superlou/deskbot/cad/HXT900/hxt900.png

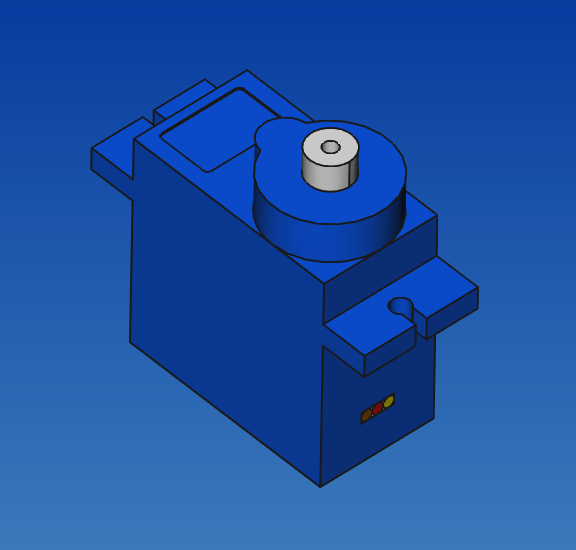
cad/HXT900/hxt900.png
