superlou/deskbot/blender/mockup.blend.png

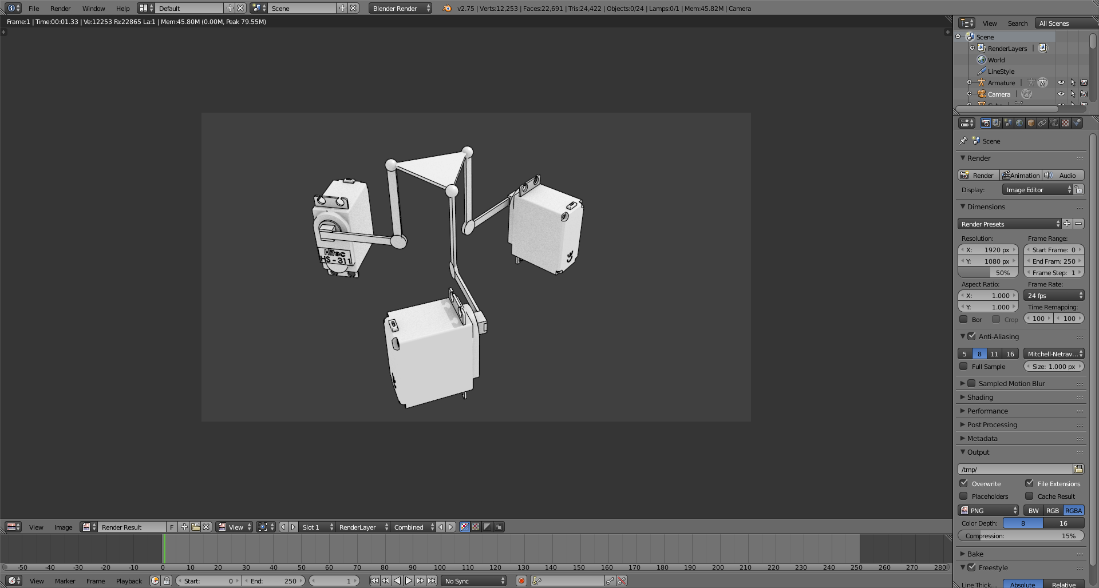
blender/mockup.blend.png
