superlou/deskbot/blender/sketch_render.png

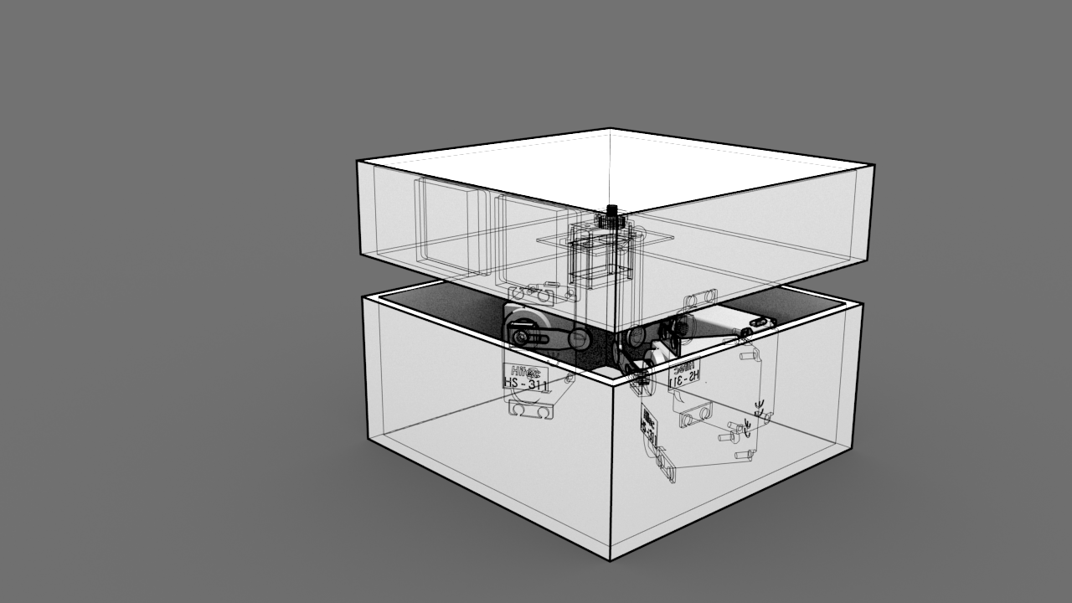
blender/sketch_render.png
