superlou/deskbot/blender/sketch_render_no_box.png

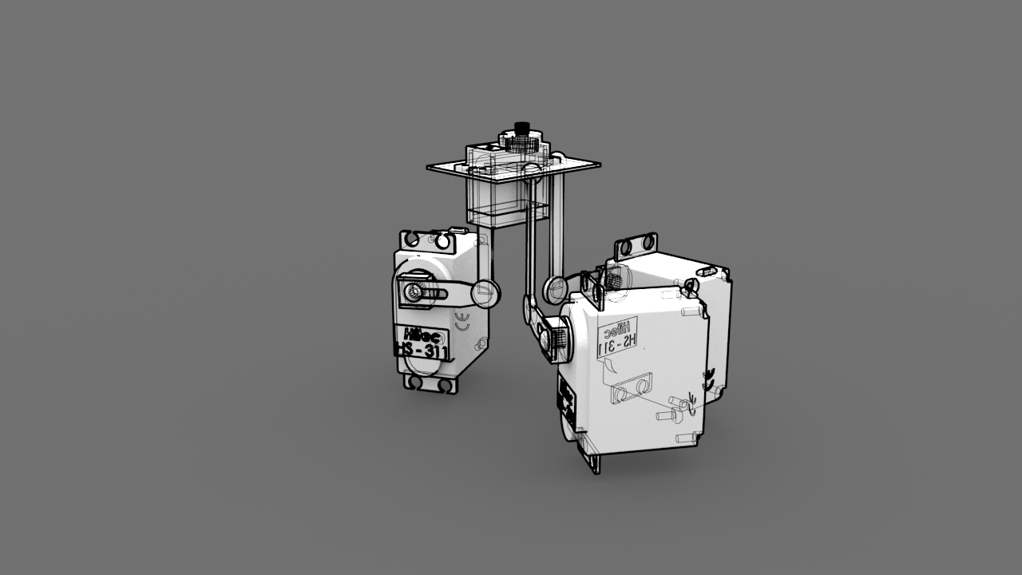
blender/sketch_render_no_box.png
