superlou/deskbot/diagrams/constrains.png

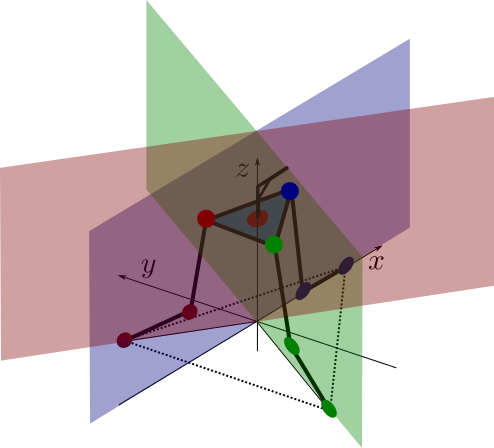
diagrams/constrains.png
