superlou/deskbot/diagrams/leg_model.png

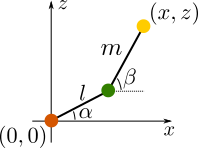
diagrams/leg_model.png
