superlou/deskbot/diagrams/leg_solutions.png

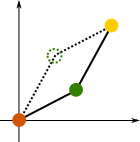
diagrams/leg_solutions.png
