superlou/deskbot/diagrams/simple_platform.png

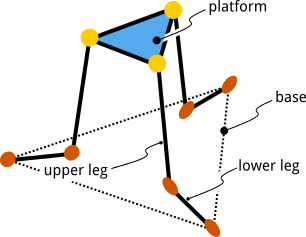
diagrams/simple_platform.png
