superlou/deskbot/cad/servo/Hitec HS-311 Servo Motor/Spline.SLDPRT

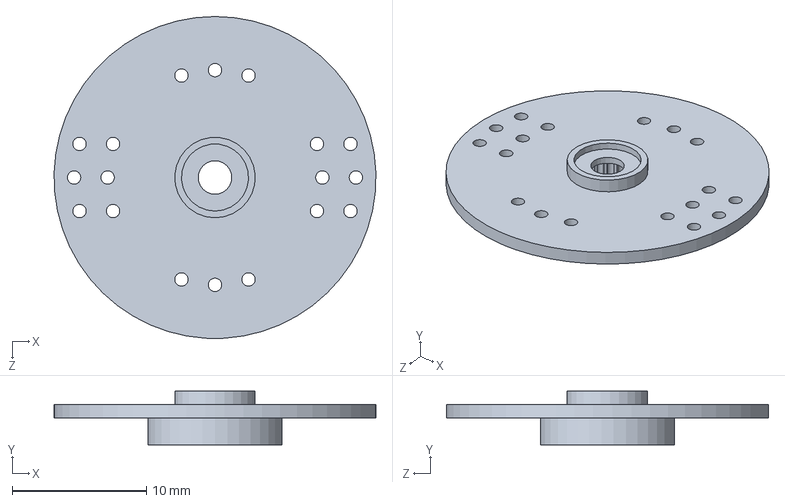
[picture p27: CAD file, 2015-07-31]
cad/servo/Hitec HS-311 Servo Motor/Spline.SLDPRT
24.0 x 4.00 x 24.0 mm
