superlou/deskbot/cad/servo_horn.fcstd

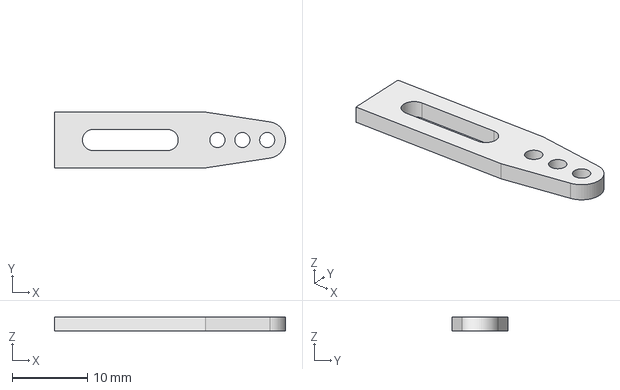
[picture p28: CAD file, 2016-11-07]
cad/servo_horn.fcstd
30.6 x 7.40 x 1.90 mm
