superlou/deskbot/cad/clevis.fcstd

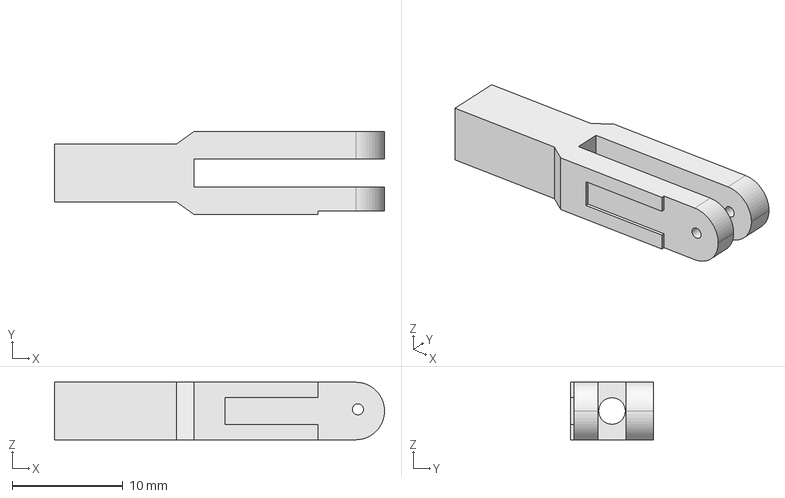
[picture p29: CAD file, 2016-11-07]
cad/clevis.fcstd
29.8 x 7.50 x 5.20 mm
