superlou/deskbot/cad/hs-311_pinion_adapter.fcstd

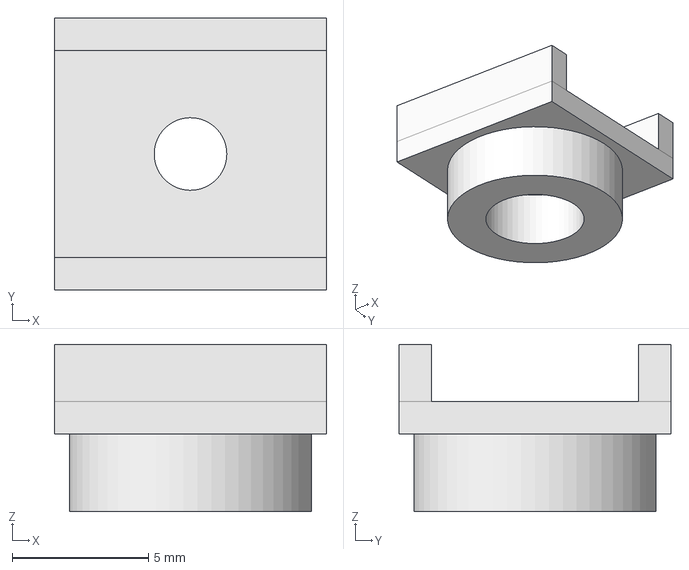
[picture p30: CAD file, 2016-11-07]
cad/hs-311_pinion_adapter.fcstd
10.0 x 10.0 x 6.15 mm
