superlou/deskbot/cad/threaded_ball.fcstd

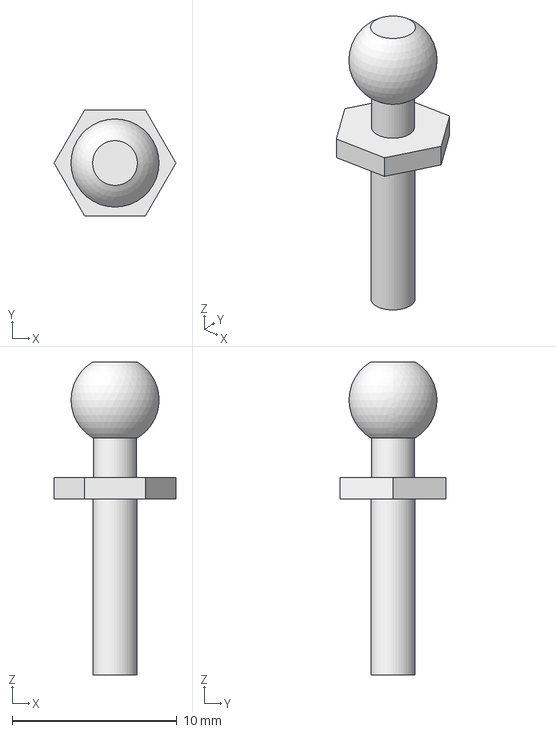
[picture p31: CAD file, 2016-11-07]
cad/threaded_ball.fcstd
7.39 x 6.40 x 19.0 mm
