superlou/deskbot/cad/base.fcstd

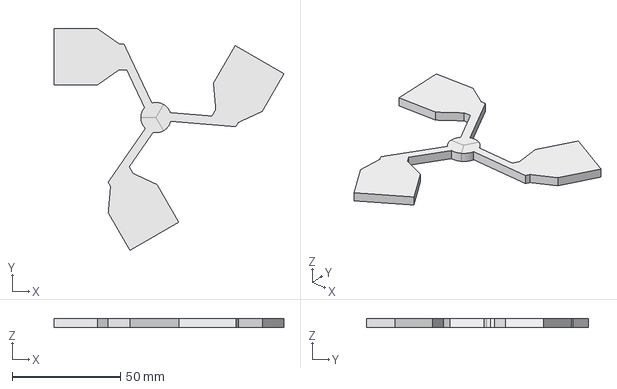
[picture p32: CAD file, 2016-07-19]
cad/base.fcstd
106.0 x 102.2 x 4.00 mm
