superlou/deskbot/cad/crown2.fcstd

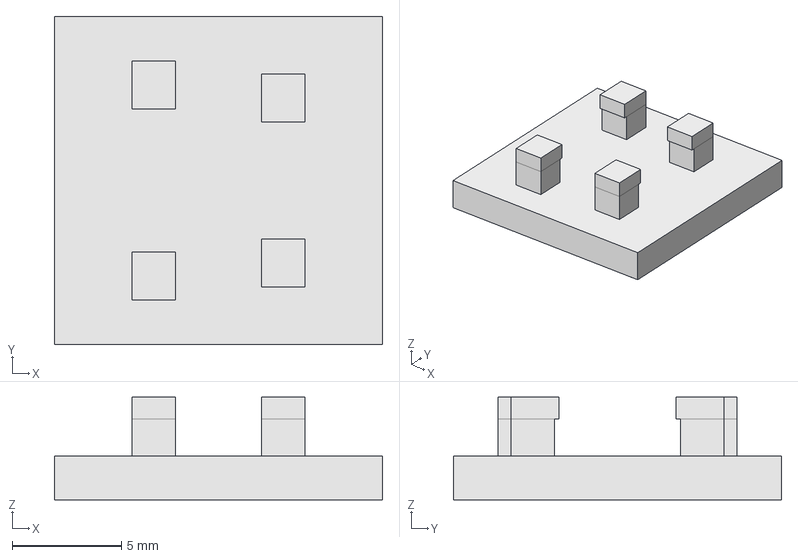
[picture p33: CAD file, 2016-07-19]
cad/crown2.fcstd
15.0 x 15.0 x 4.70 mm
