superlou/deskbot/cad/flat_servo_stand.fcstd

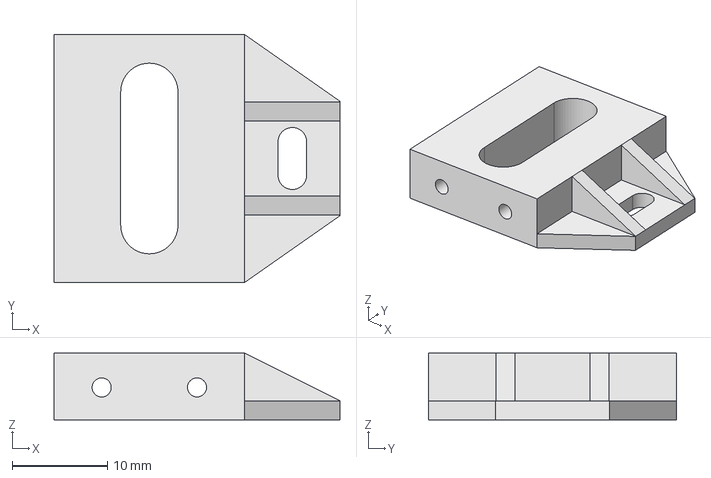
[picture p34: CAD file, 2016-07-19]
cad/flat_servo_stand.fcstd
30.0 x 26.0 x 7.00 mm
