superlou/deskbot/cad/crown.fcstd

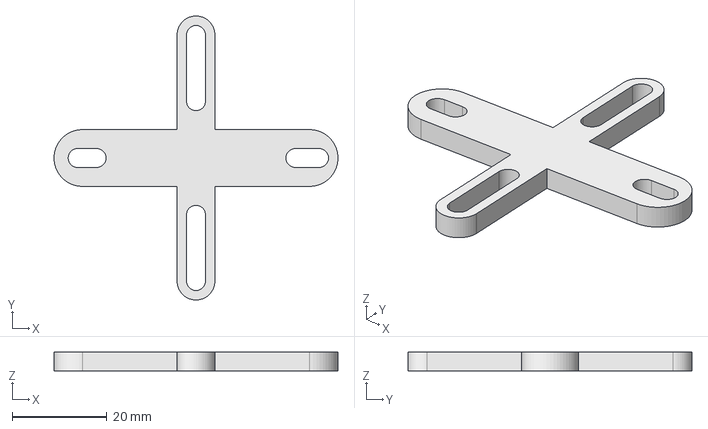
[picture p35: CAD file, 2016-07-19]
cad/crown.fcstd
60.0 x 60.0 x 4.00 mm
