superlou/deskbot/cad/plate.stl

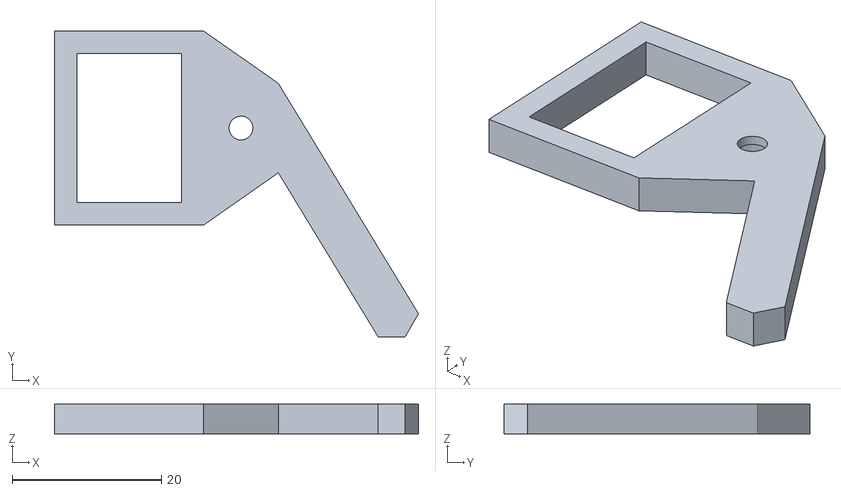
[picture p36: CAD file, 2016-07-19]
cad/plate.stl
48.8 x 41.0 x 4.00
