superlou/deskbot/cad/servo_and_flat_stand.fcstd

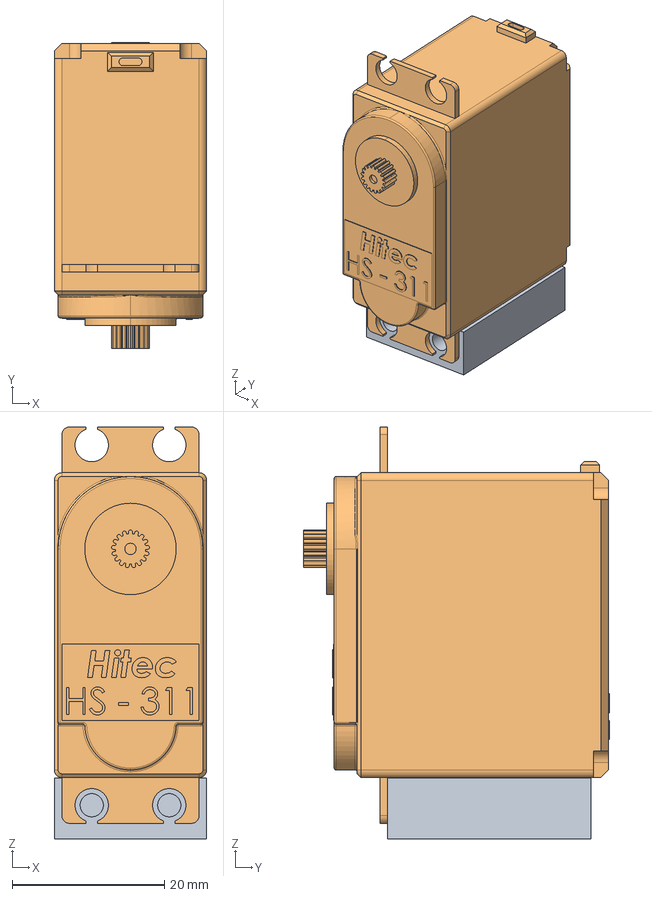
[picture p37: CAD file, 2016-04-03]
cad/servo_and_flat_stand.fcstd
20.0 x 40.1 x 54.1 mm
flat_servo_stand_01
servo_hs_311_01
