superlou/deskbot/cad/thin_servo_stand.fcstd

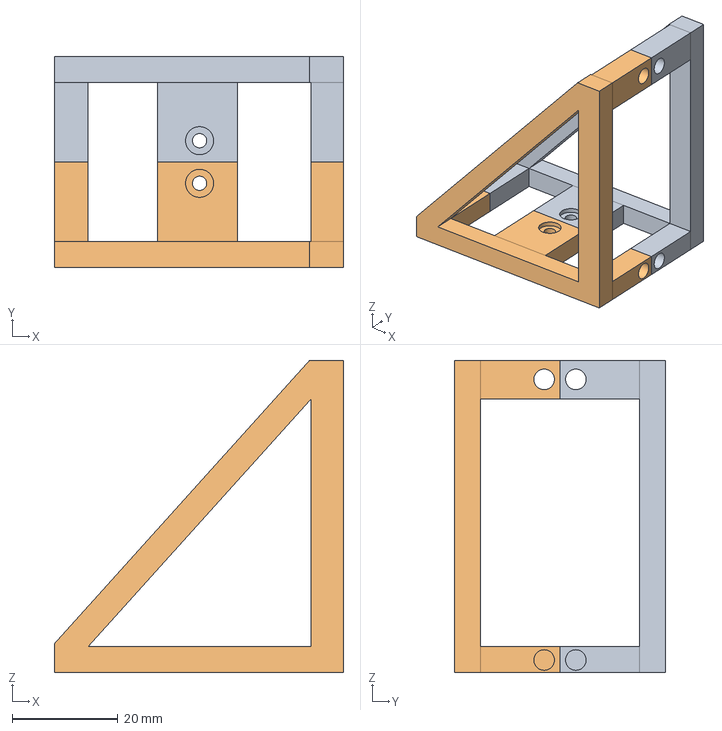
[picture p38: CAD file, 2015-12-17]
cad/thin_servo_stand.fcstd
54.8 x 40.0 x 59.0 mm
Pocket002 (Mirror #1)
