superlou/deskbot/cad/test_mount.step

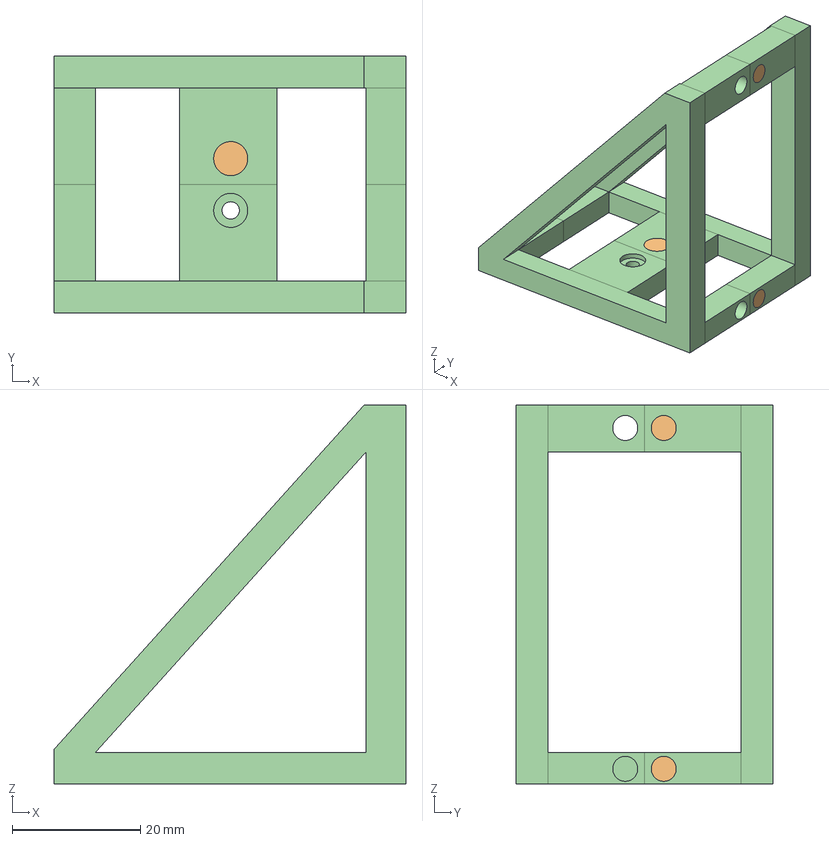
[picture p39: CAD file, 2015-12-17]
cad/test_mount.step
54.8 x 40.0 x 59.0 mm
