superlou/deskbot/cad/simple_stand.fcstd

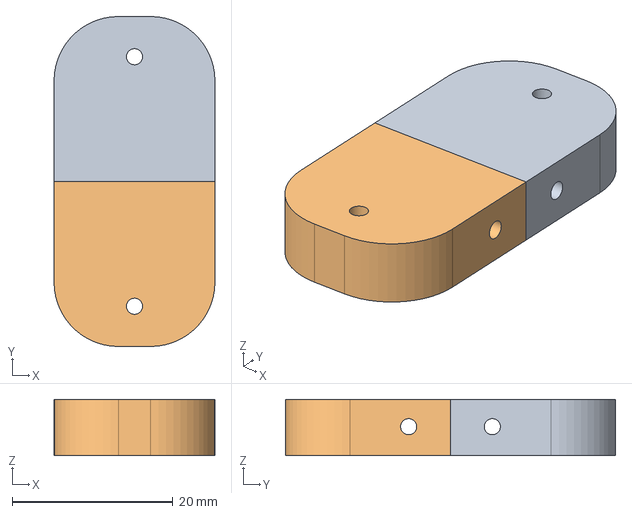
[picture p40: CAD file, 2015-10-16]
cad/simple_stand.fcstd
20.0 x 41.0 x 7.00 mm
Fillet (Mirror #1)
