superlou/deskbot/cad/vertical_servo_stand.fcstd

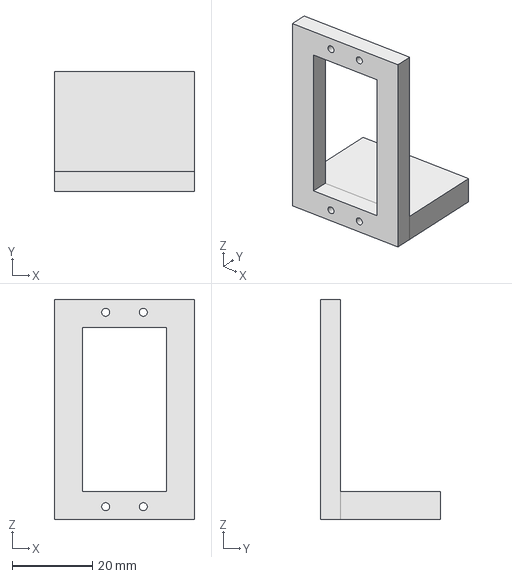
[picture p41: CAD file, 2015-08-23]
cad/vertical_servo_stand.fcstd
35.0 x 30.0 x 55.0 mm
