superlou/deskbot/cad/socket_pin.fcstd

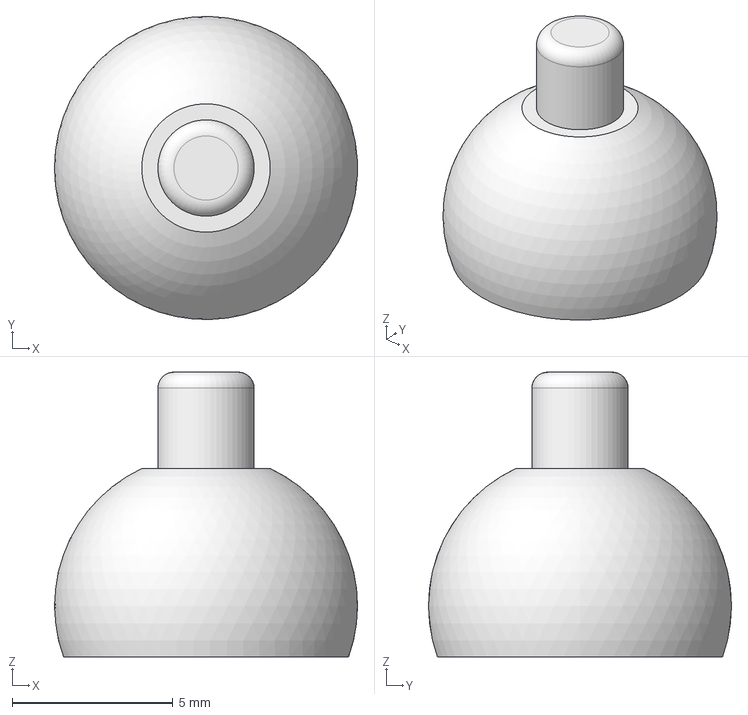
[picture p42: CAD file, 2015-08-01]
cad/socket_pin.fcstd
9.44 x 9.44 x 8.87 mm
