superlou/deskbot/cad/head_mount_flat.fcstd

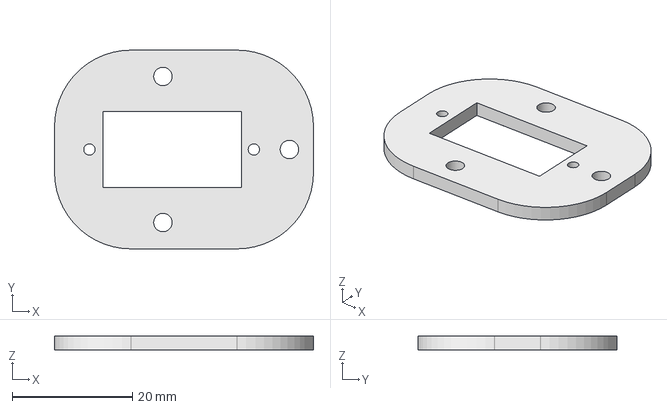
[picture p43: CAD file, 2015-08-01]
cad/head_mount_flat.fcstd
43.0 x 33.0 x 2.40 mm
