superlou/deskbot/cad/horn.fcstd

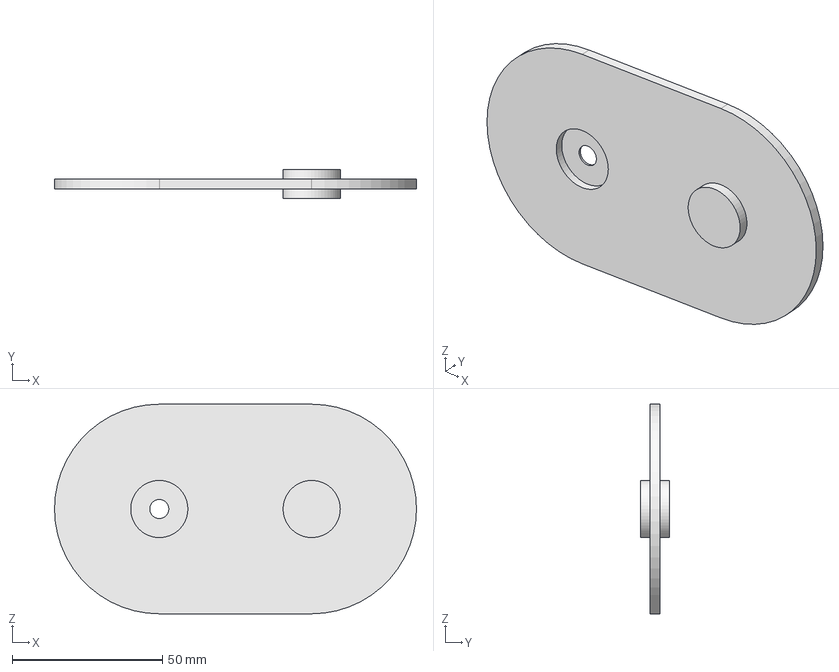
[picture p44: CAD file, 2015-07-31]
cad/horn.fcstd
120.6 x 9.53 x 69.8 mm
