superlou/deskbot/cad/head_mount.fcstd

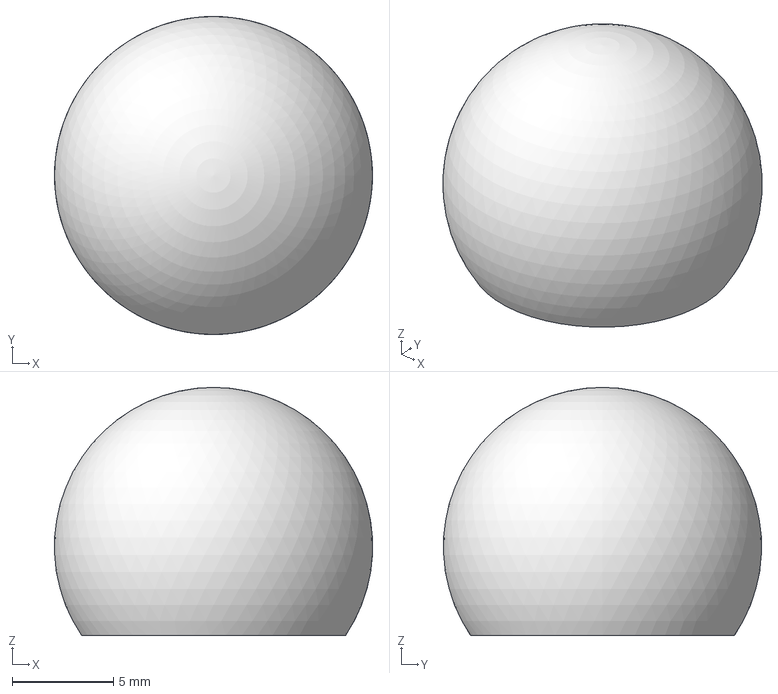
[picture p45: CAD file, 2015-07-31]
cad/head_mount.fcstd
15.7 x 15.7 x 12.2 mm
