superlou/deskbot/cad/arm.fcstd

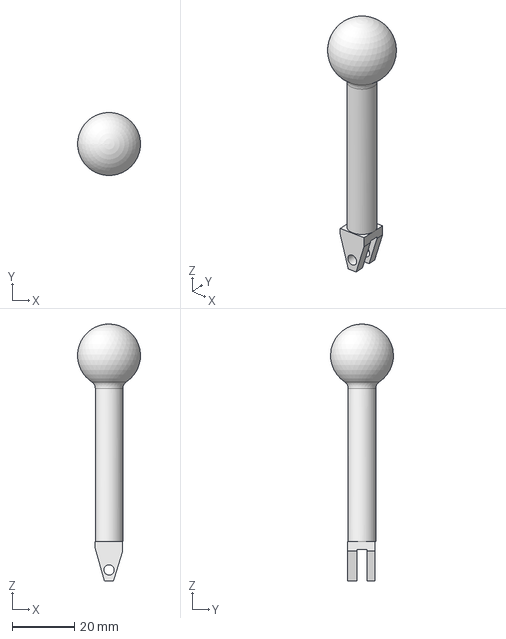
[picture p46: CAD file, 2015-07-31]
cad/arm.fcstd
20.3 x 20.2 x 82.8 mm
