superlou/deskbot/cad/test_horn.step

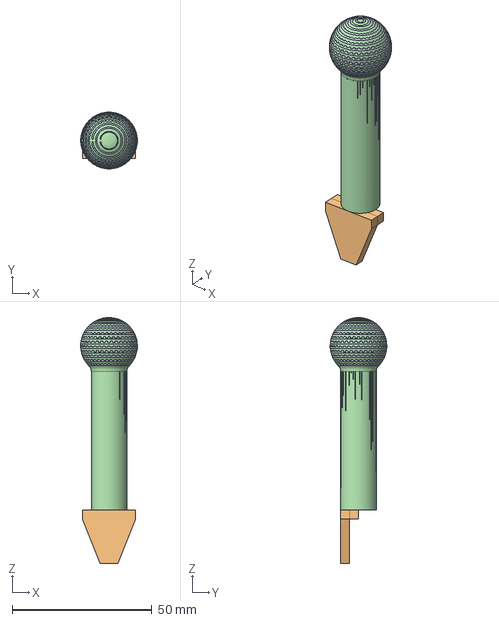
[picture p47: CAD file, 2015-07-31]
cad/test_horn.step
20.3 x 20.3 x 87.9 mm
